thorrockstar/pulsar_p3_repmod_odin/Hardware/Eagle/loki/loki_mod_bottom.png

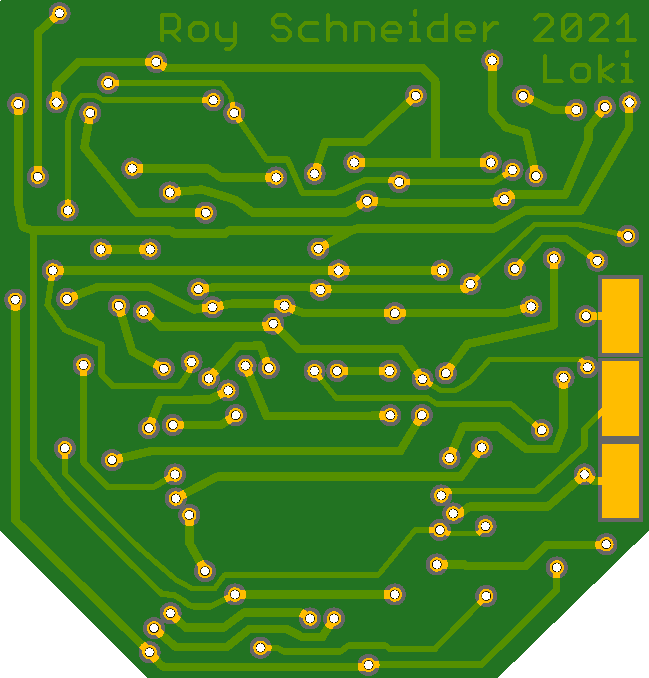
Hardware/Eagle/loki/loki_mod_bottom.png
