thorrockstar/pulsar_p3_repmod_odin/Hardware/Eagle/odin_mod_top.png

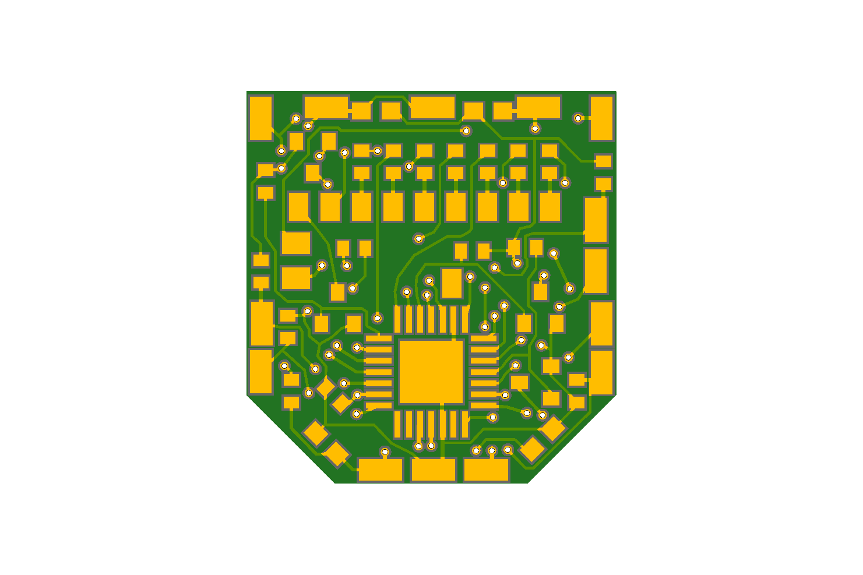
Hardware/Eagle/odin_mod_top.png
