thorrockstar/pulsar_p3_repmod_odin/Hardware/Eagle/p4mod/sif/sif6.jpg

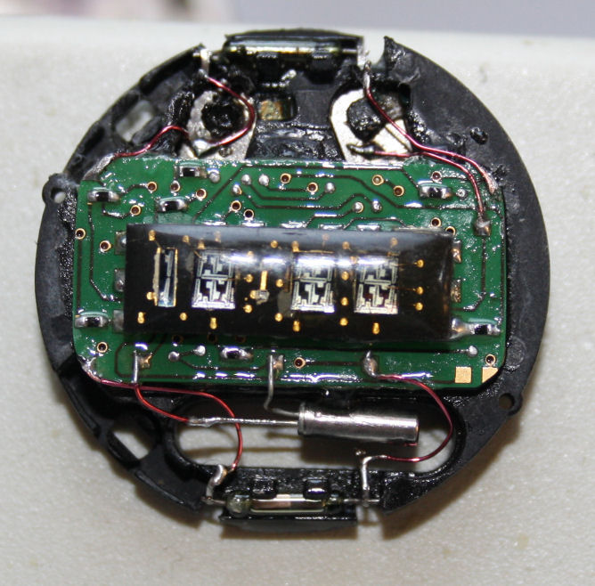
Hardware/Eagle/p4mod/sif/sif6.jpg
