thorrockstar/pulsar_p3_repmod_odin/Hardware/Eagle/p4mod/sif/sif7.jpg

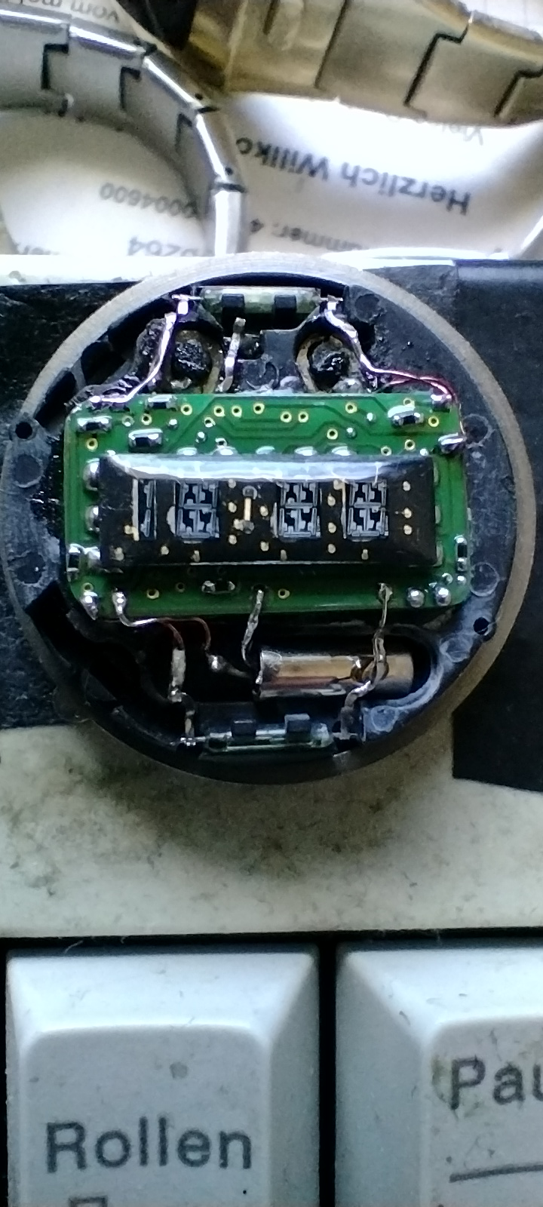
Hardware/Eagle/p4mod/sif/sif7.jpg
