thorrockstar/pulsar_p3_repmod_odin/Hardware/Eagle/p4mod/sif/sif_mk2.png

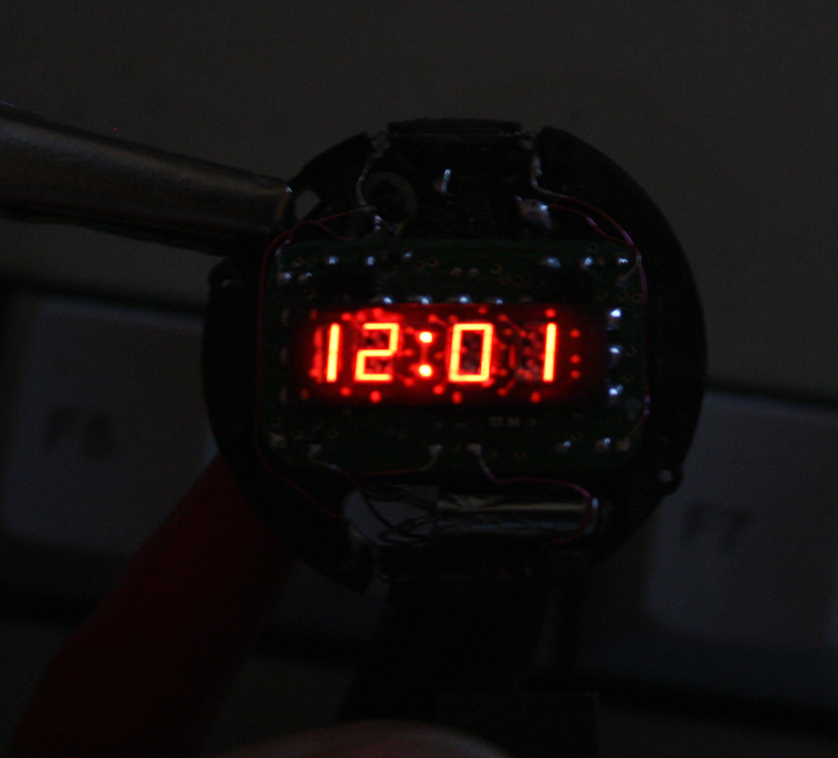
Hardware/Eagle/p4mod/sif/sif_mk2.png
