thorrockstar/pulsar_p3_repmod_odin/Hardware/Eagle/p4mod/sif/sif_mkII_1.jpg

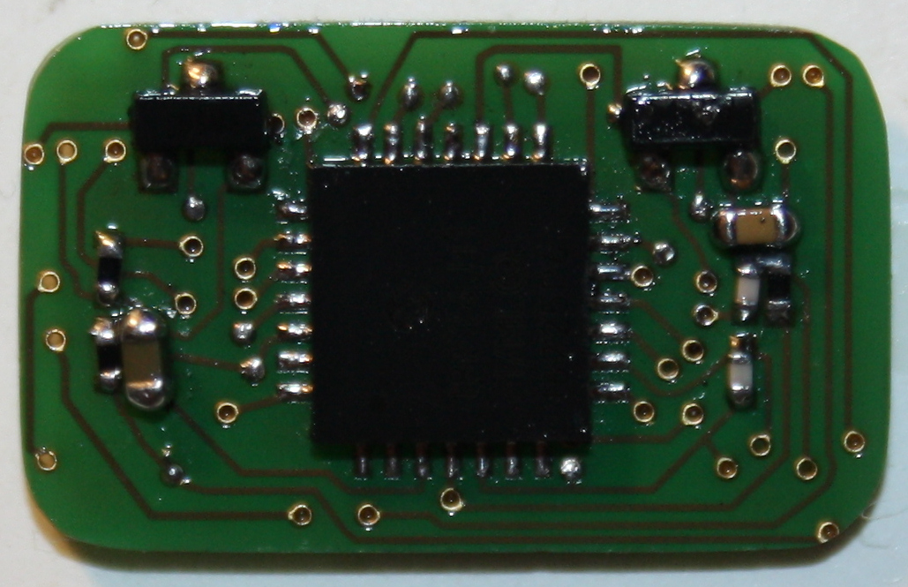
Hardware/Eagle/p4mod/sif/sif_mkII_1.jpg
