thorrockstar/pulsar_p3_repmod_odin/Hardware/Eagle/p4mod/sif/sif_mod_top.png

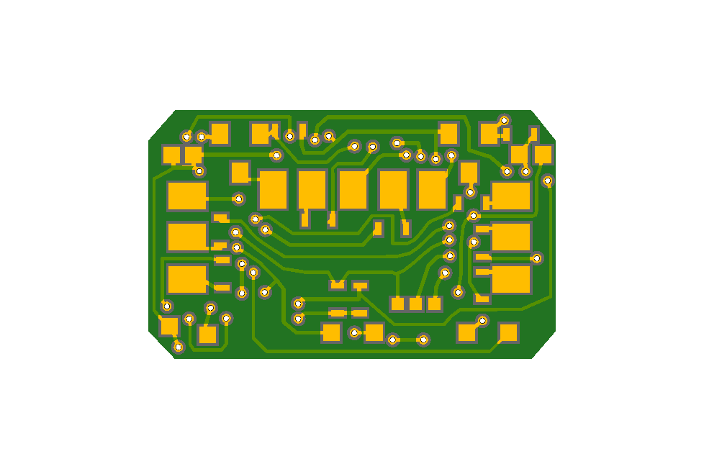
Hardware/Eagle/p4mod/sif/sif_mod_top.png
