thorrockstar/pulsar_p3_repmod_odin/p3_odin_mark_ii_with_display.png

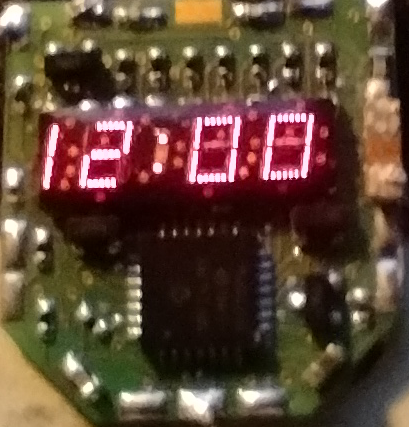
p3_odin_mark_ii_with_display.png
