thorrockstar/pulsar_p3_repmod_odin/p3_odin_second.png

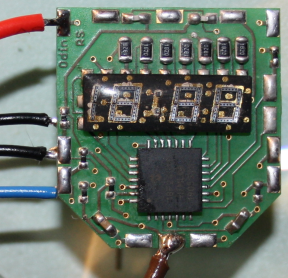
p3_odin_second.png
