thorrockstar/pulsar_p3_repmod_odin/p3_odin_updated.png

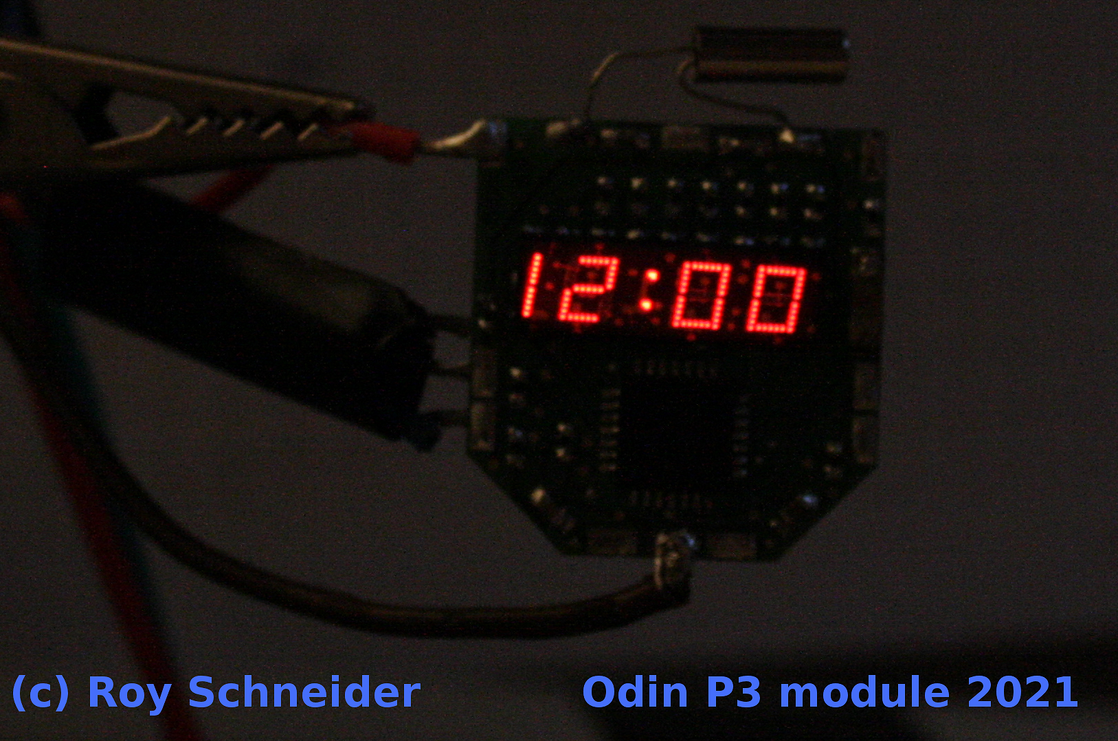
p3_odin_updated.png
