thorrockstar/pulsar_p3_repmod_odin/p3loki_hires.png

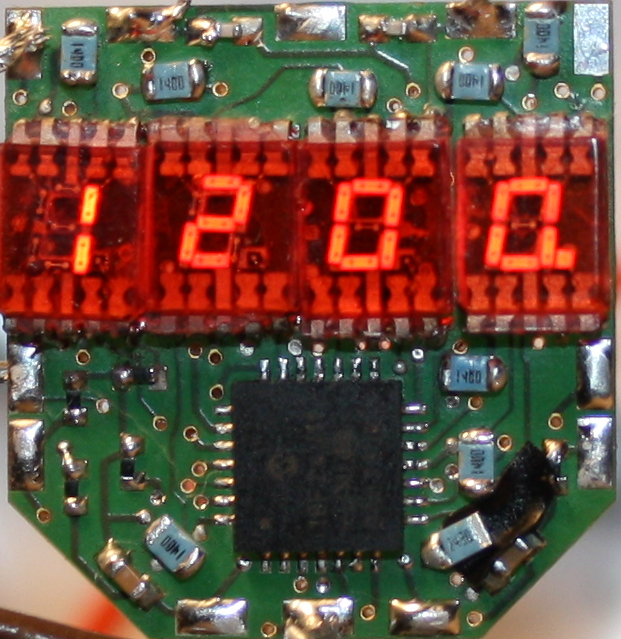
p3loki_hires.png
