thorrockstar/pulsar_p3_repmod_odin/p3odin_hires.jpg

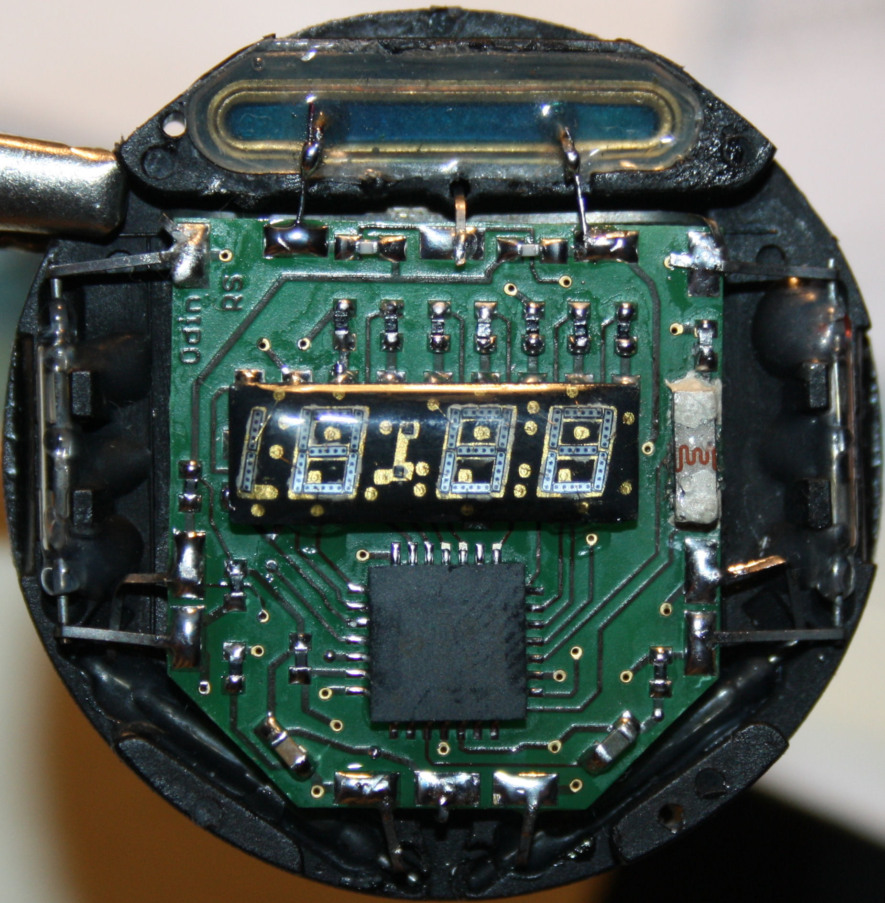
p3odin_hires.jpg
