thorrockstar/pulsar_p3_repmod_odin/Pulsar_P3_Loki_Module.jpg

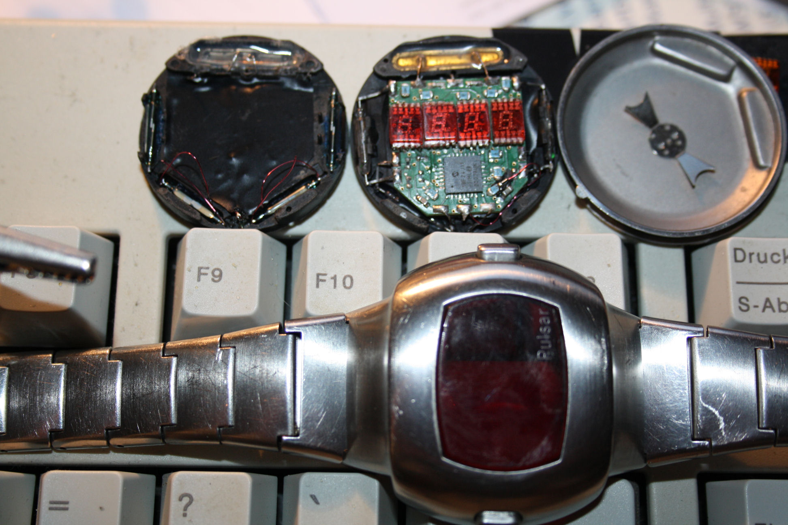
Pulsar_P3_Loki_Module.jpg
