thorrockstar/pulsar_p3_repmod_odin/Pulsar_P3_Odin_Module.jpg

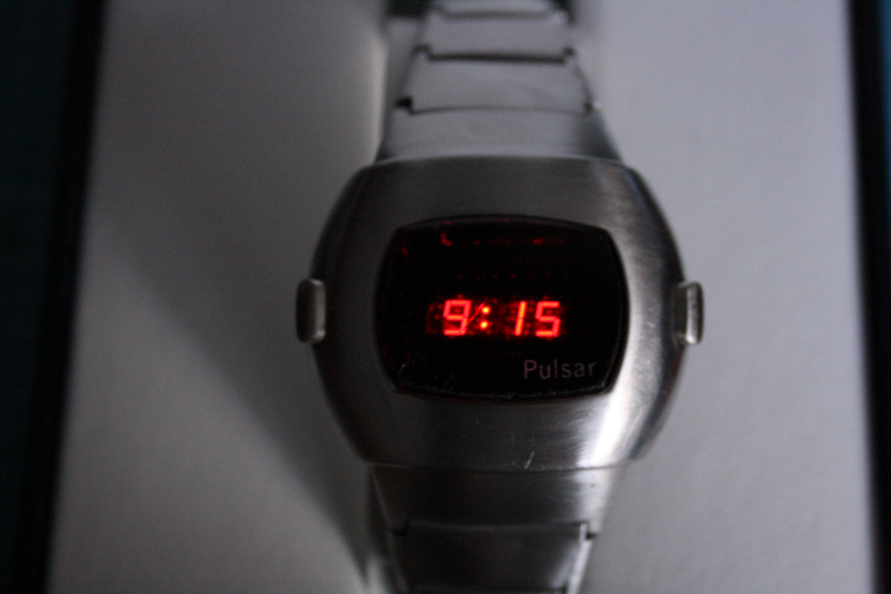
Pulsar_P3_Odin_Module.jpg
